raszpl/FIC-486-GAC-2-Cache-Module/doc/vlb-edge-conn.png

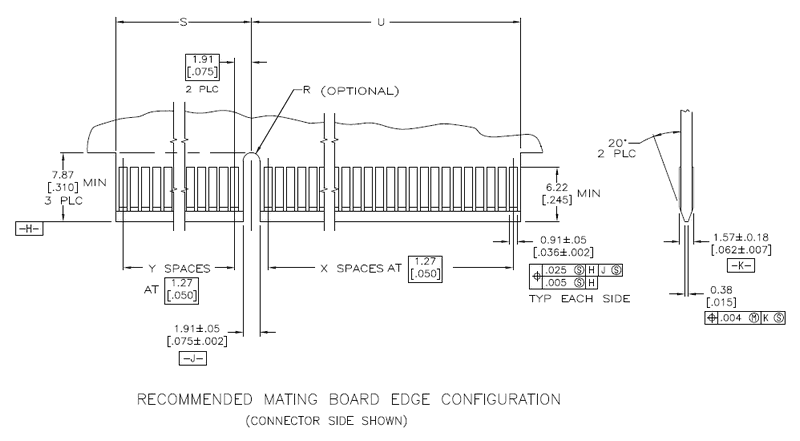
doc/vlb-edge-conn.png
