raszpl/FIC-486-GAC-2-Cache-Module/doc/VLB_pins.png

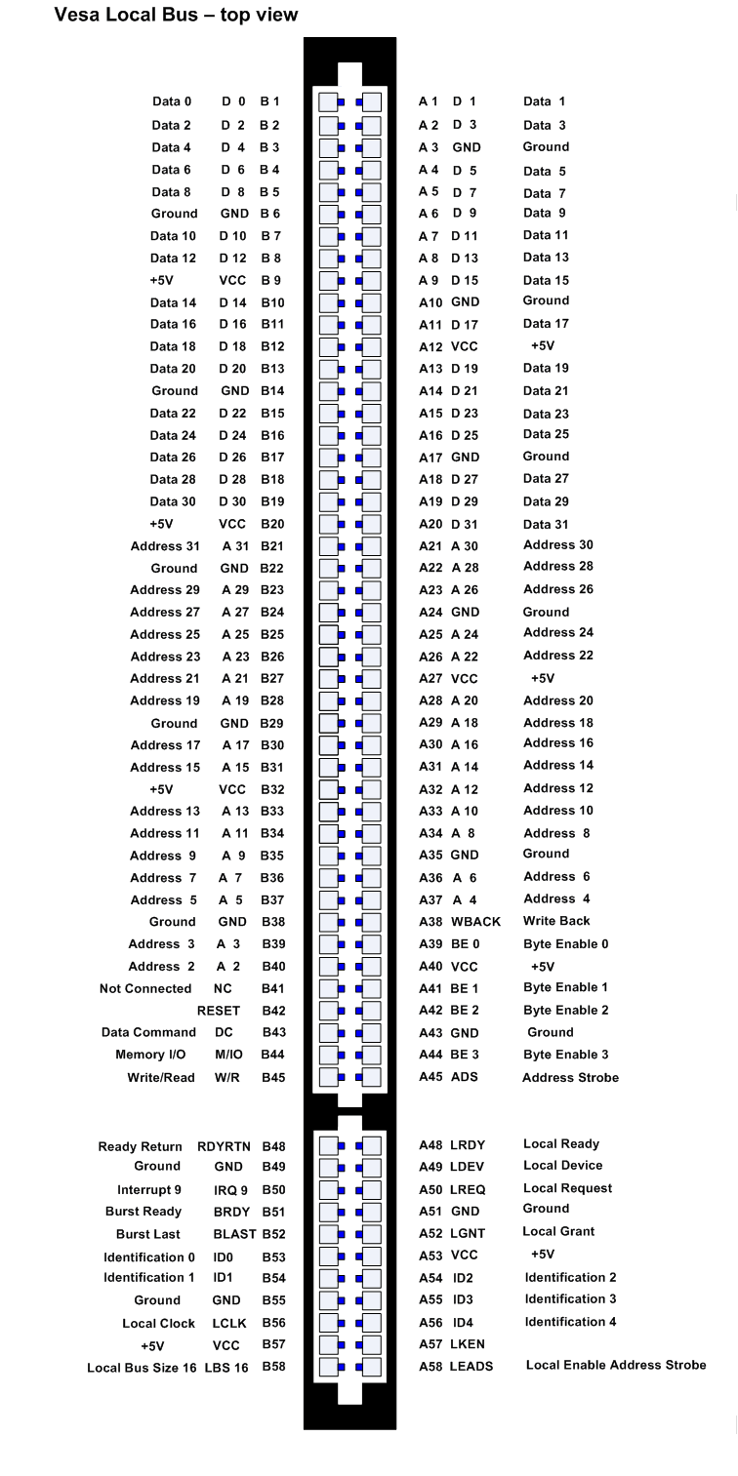
doc/VLB_pins.png
