raszpl/FIC-486-GAC-2-Cache-Module/img/FIC 486-GAC-2 cache coast VIP 95%.png

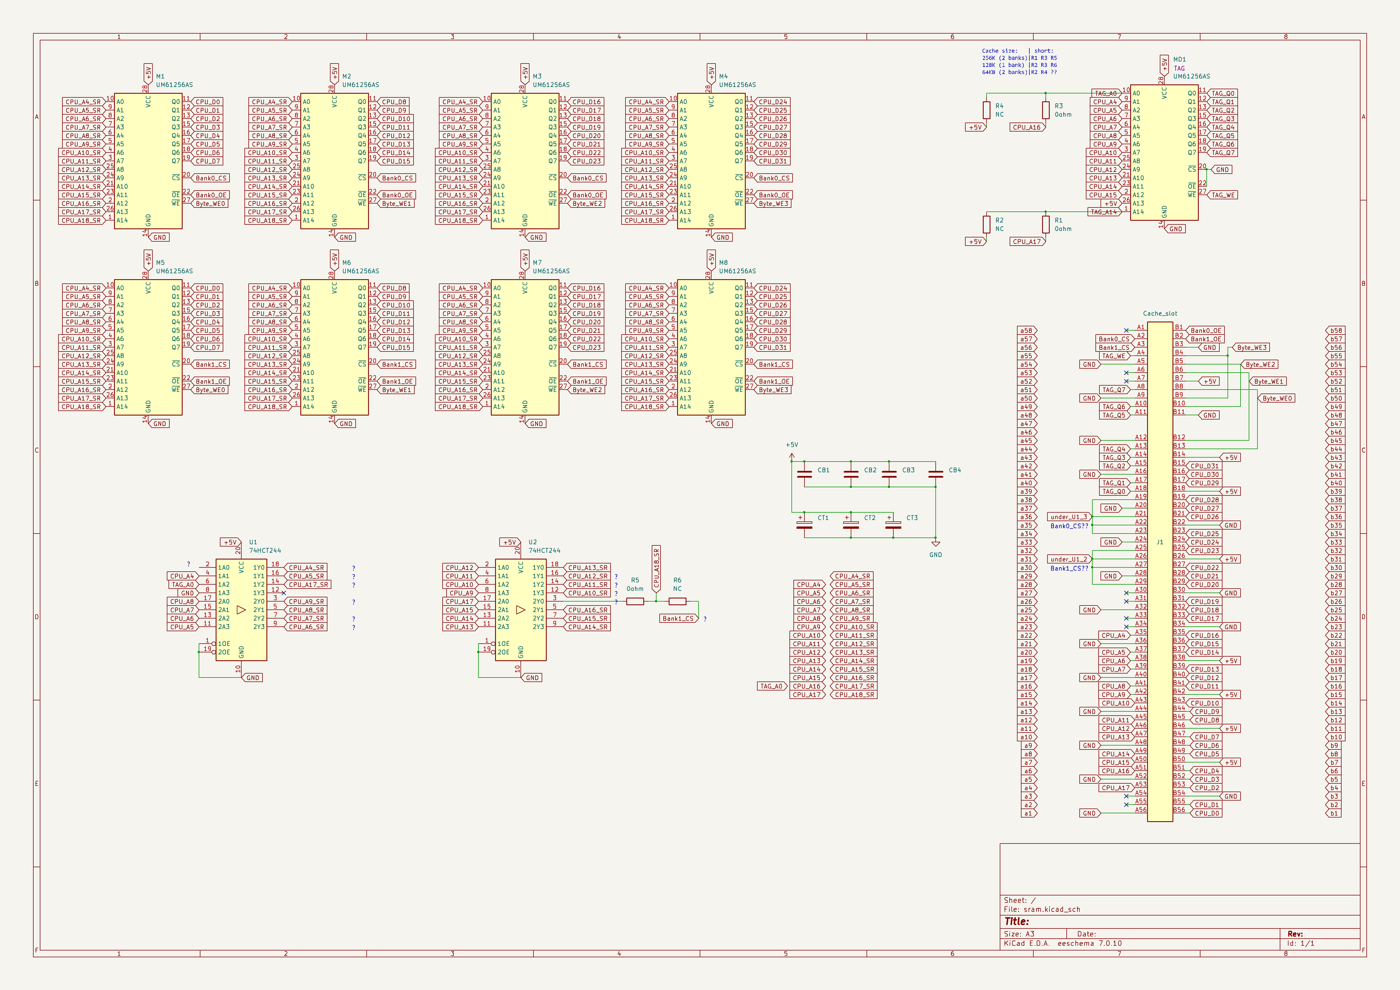
img/FIC 486-GAC-2 cache coast VIP 95%.png
