raszpl/FIC-486-GAC-2-Cache-Module/img/FIC 486-GAC-2 cache Final rev2.4.png

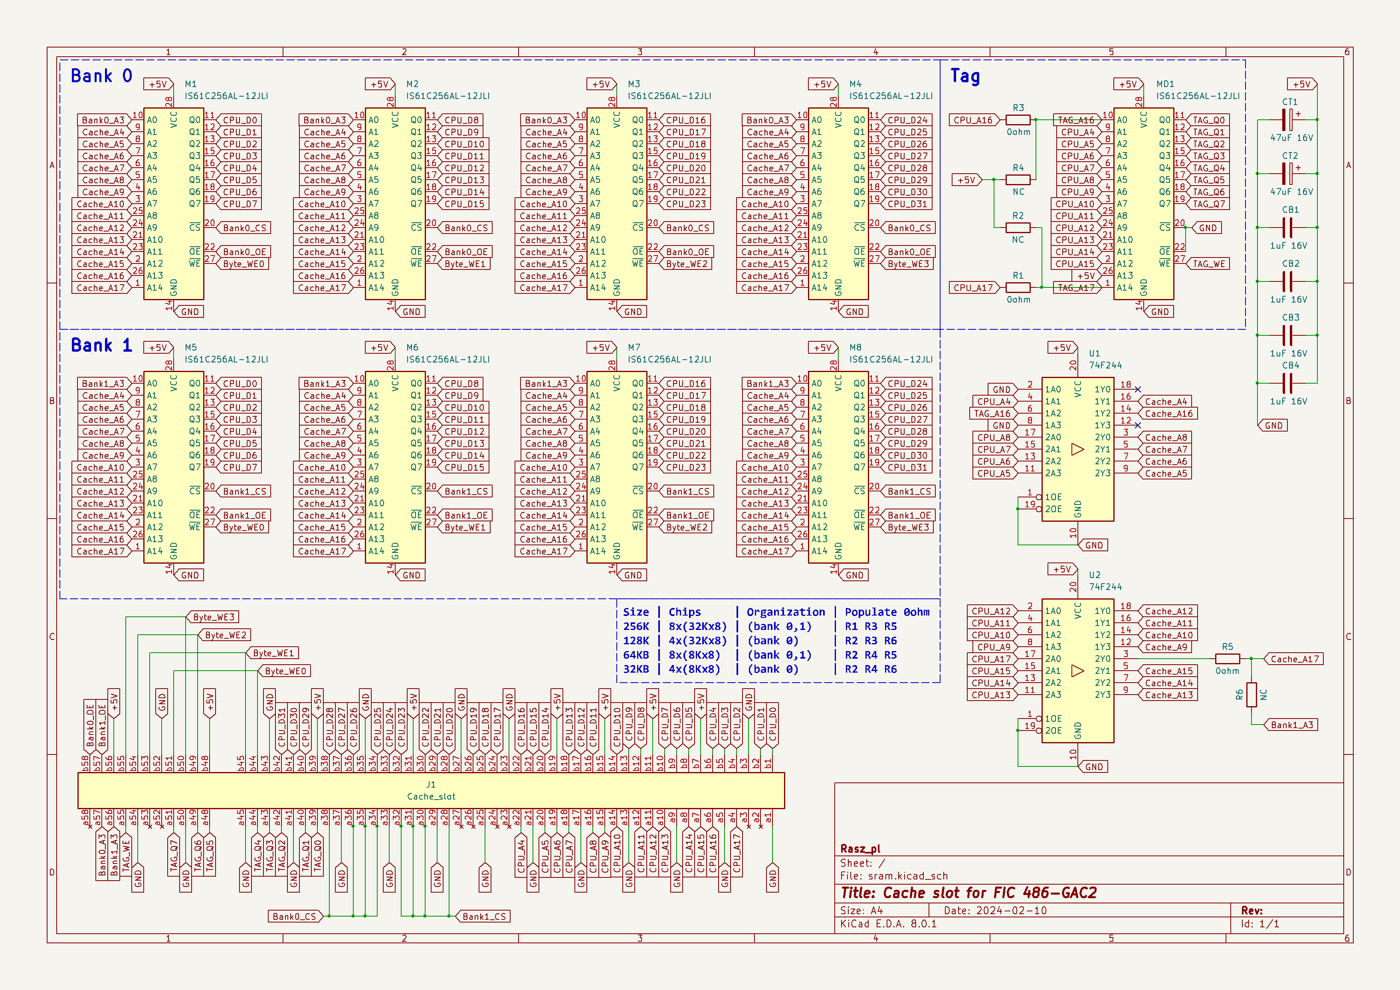
img/FIC 486-GAC-2 cache Final rev2.4.png
