raszpl/FIC-486-GAC-2-Cache-Module/img/front render.png

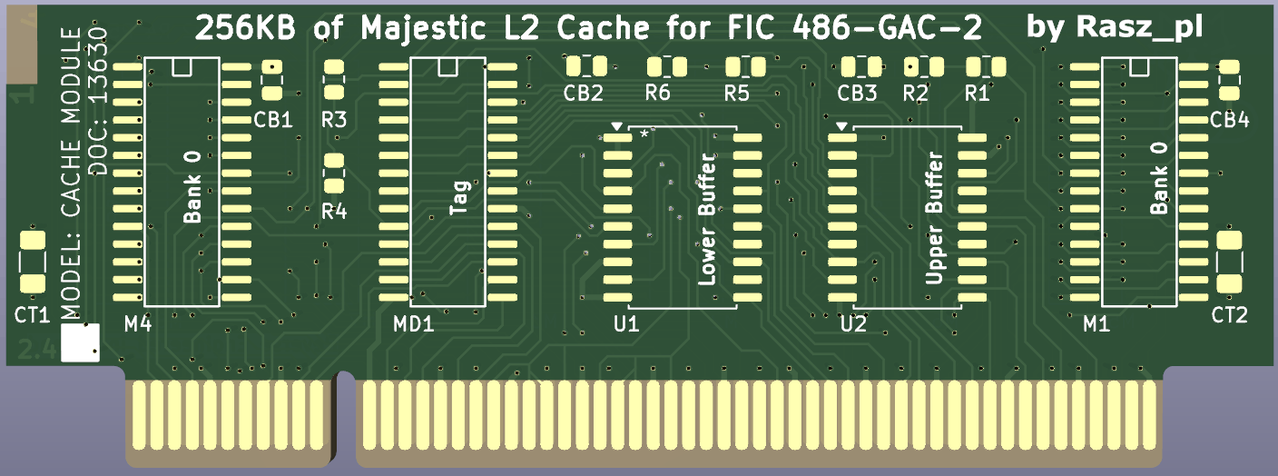
img/front render.png
