raszpl/FIC-486-GAC-2-Cache-Module/not compatible proprietary vlb cache modules/7MP6152.jpg

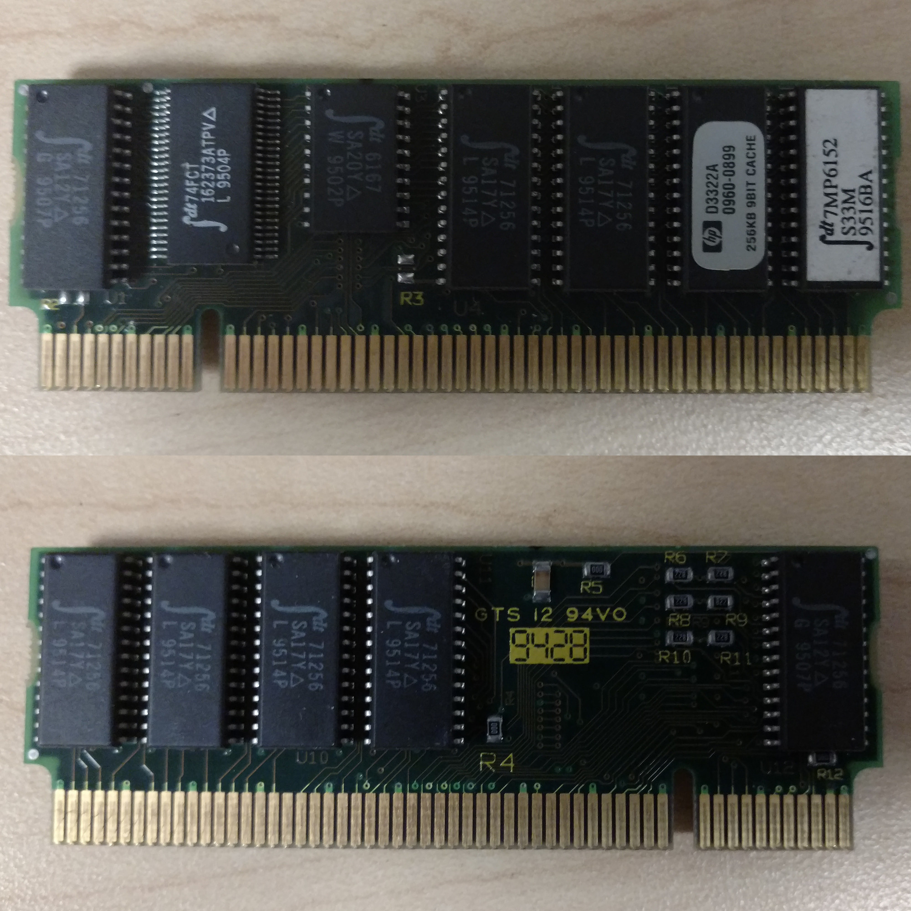
not compatible proprietary vlb cache modules/7MP6152.jpg
