raszpl/FIC-486-GAC-2-Cache-Module/not compatible proprietary vlb cache modules/ATT-Globalyst_550_575.jpg

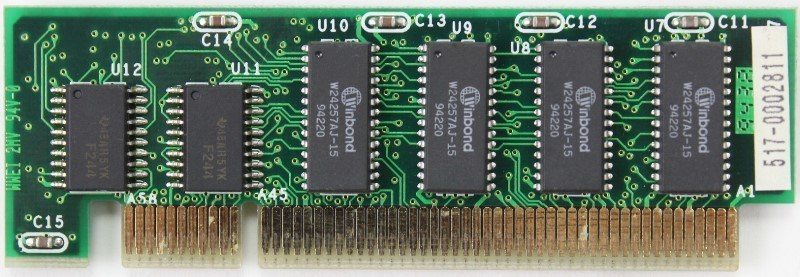
not compatible proprietary vlb cache modules/ATT-Globalyst_550_575.jpg
