raszpl/FIC-486-GAC-2-Cache-Module/not compatible proprietary vlb cache modules/Compaq 002754-001 back.jpg

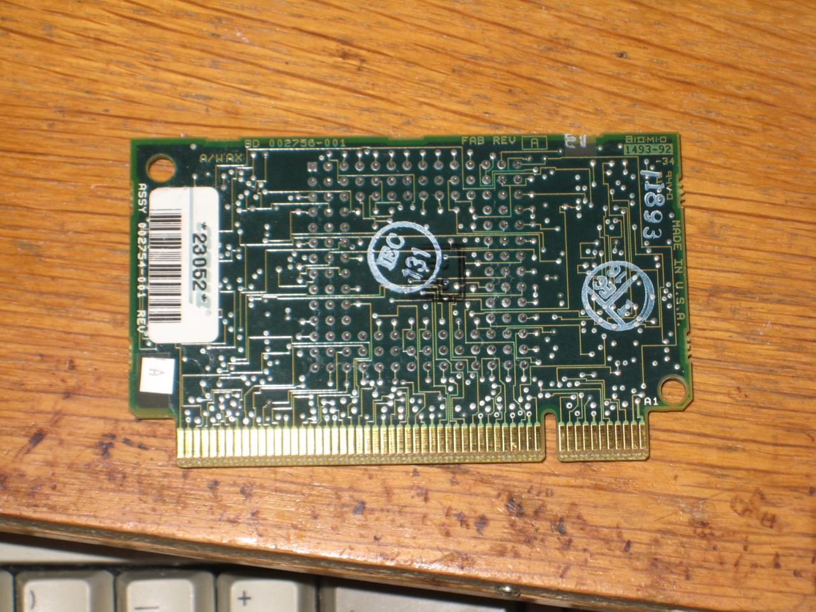
not compatible proprietary vlb cache modules/Compaq 002754-001 back.jpg
