raszpl/FIC-486-GAC-2-Cache-Module/not compatible proprietary vlb cache modules/Compaq 194380-001.jpg

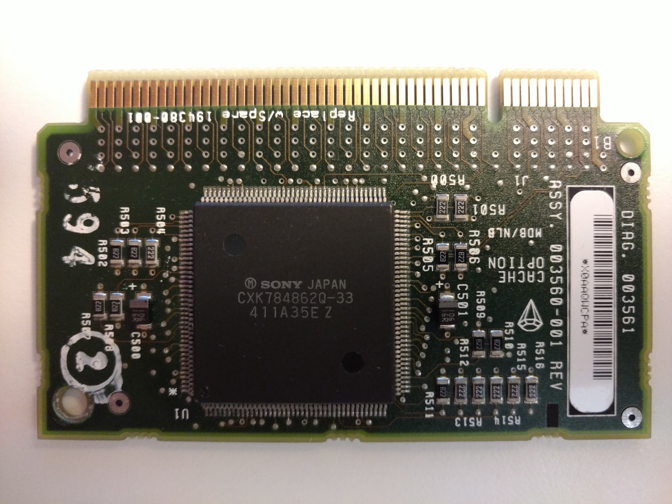
not compatible proprietary vlb cache modules/Compaq 194380-001.jpg
