raszpl/FIC-486-GAC-2-Cache-Module/not compatible proprietary vlb cache modules/Compaq 197005-001 back.jpg

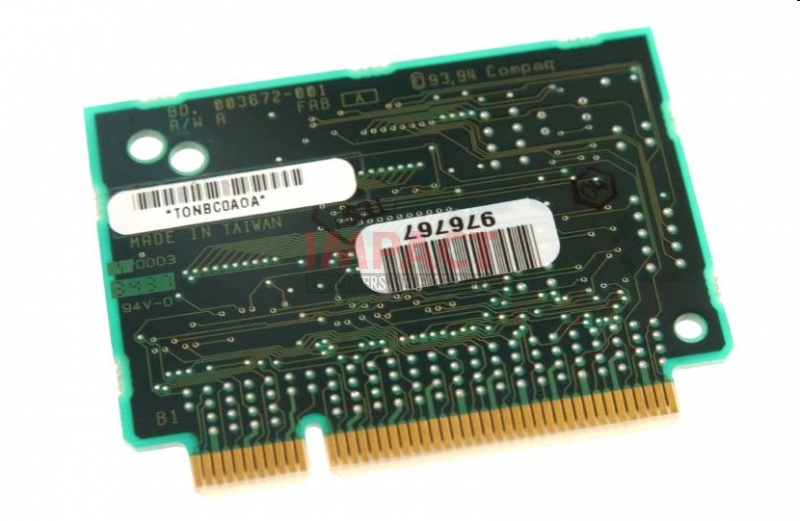
not compatible proprietary vlb cache modules/Compaq 197005-001 back.jpg
