raszpl/FIC-486-GAC-2-Cache-Module/not compatible proprietary vlb cache modules/CYM9236 back.jpg

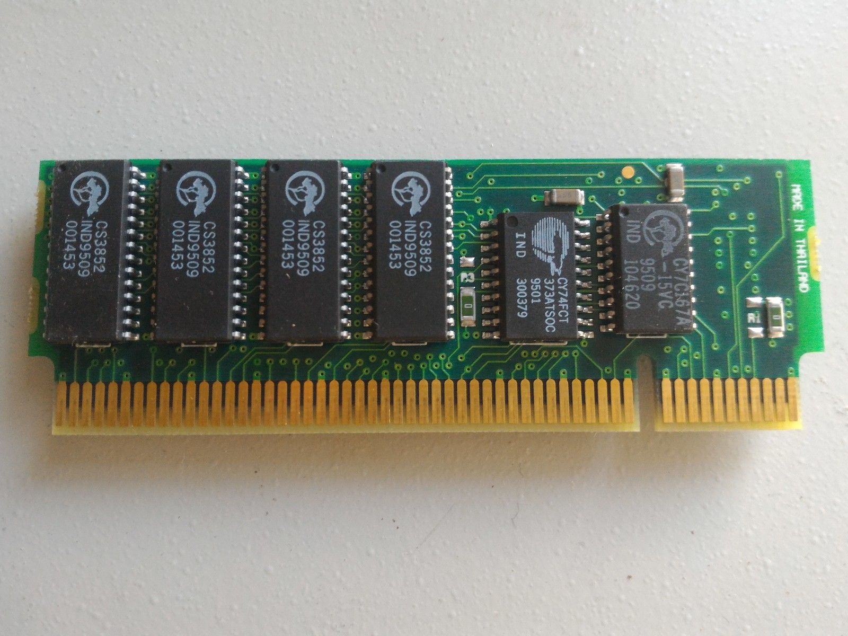
not compatible proprietary vlb cache modules/CYM9236 back.jpg
