raszpl/FIC-486-GAC-2-Cache-Module/not compatible proprietary vlb cache modules/HP Vectra VE 4 256 KB Cache D2465A back.webp

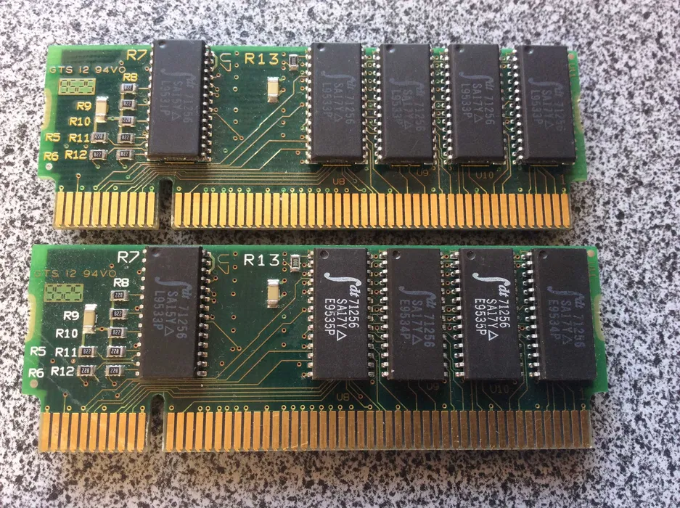
not compatible proprietary vlb cache modules/HP Vectra VE 4 256 KB Cache D2465A back.webp
