raszpl/FIC-486-GAC-2-Cache-Module/not compatible proprietary vlb cache modules/Kingston KTC-4358 inside deskpro-xe-486.jpg

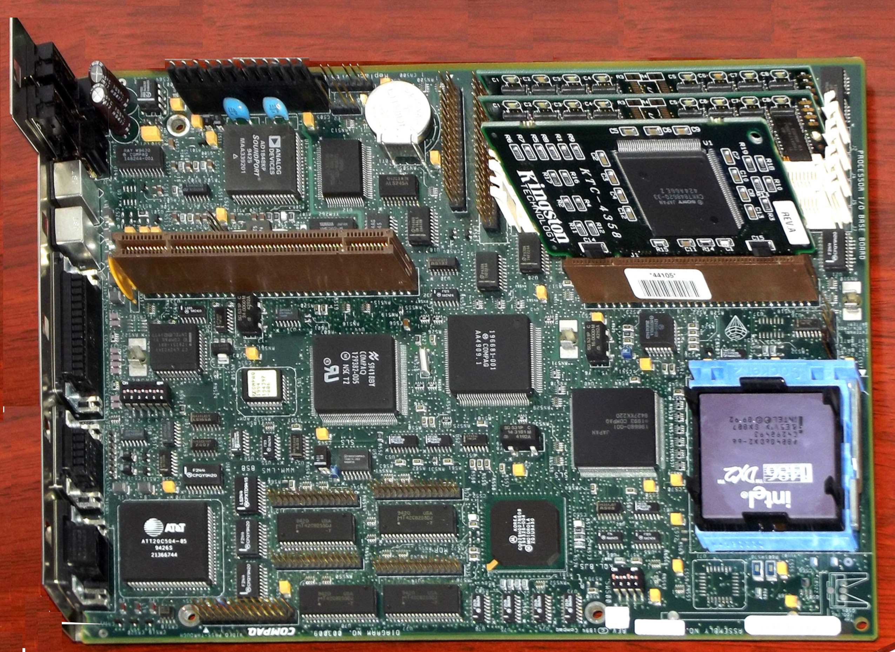
not compatible proprietary vlb cache modules/Kingston KTC-4358 inside deskpro-xe-486.jpg
