raszpl/FIC-486-GAC-2-Cache-Module/not compatible proprietary vlb cache modules/Siemens Nixdorf FD200 D882 cym9252pb.JPG

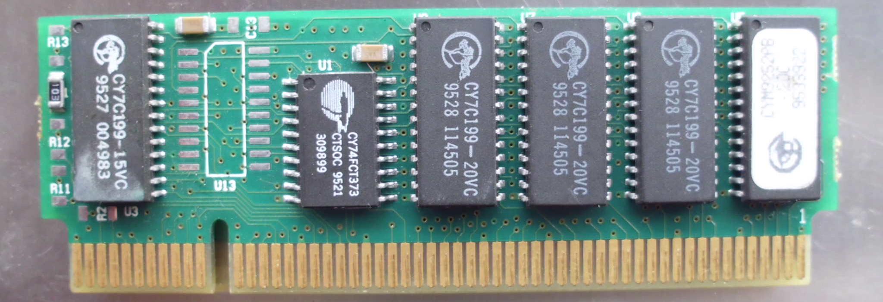
not compatible proprietary vlb cache modules/Siemens Nixdorf FD200 D882 cym9252pb.JPG
